Horse-5-333/twins/gerber-drill/twins-left/yg/GBR_8921560_1_snapshot.png

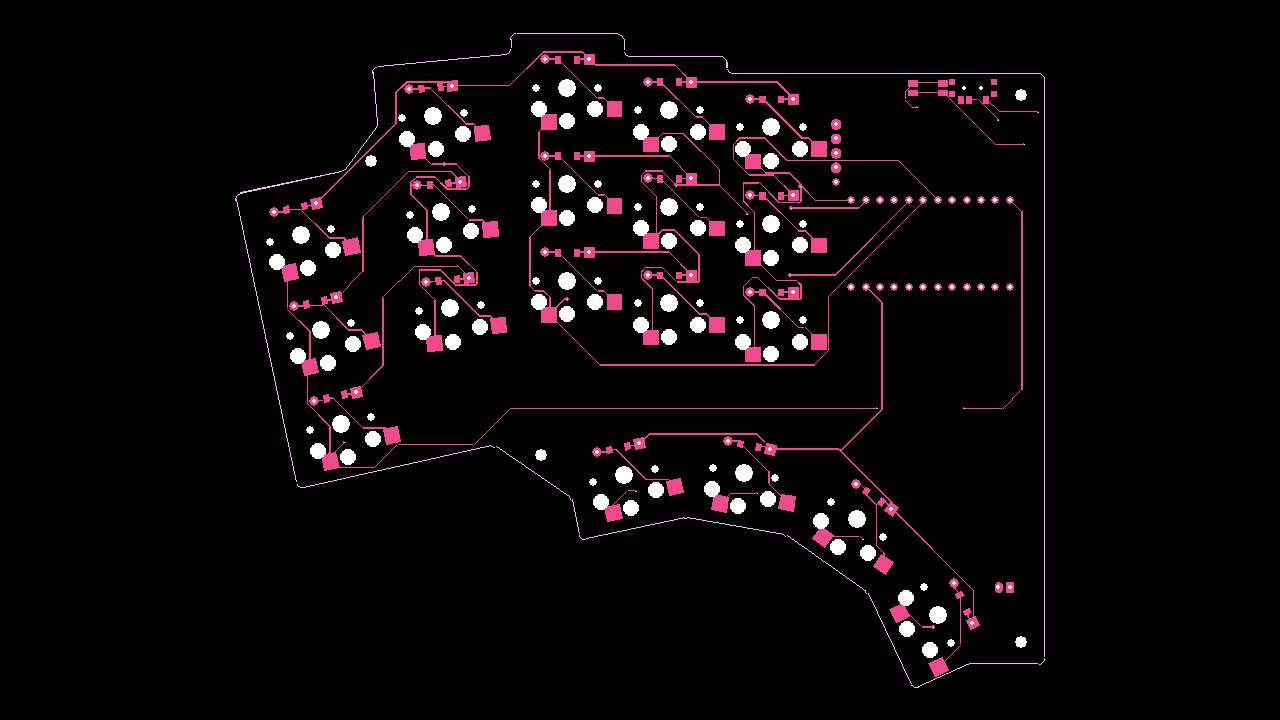
gerber-drill/twins-left/yg/GBR_8921560_1_snapshot.png
