Horse-5-333/twins/IMG_1064.jpeg

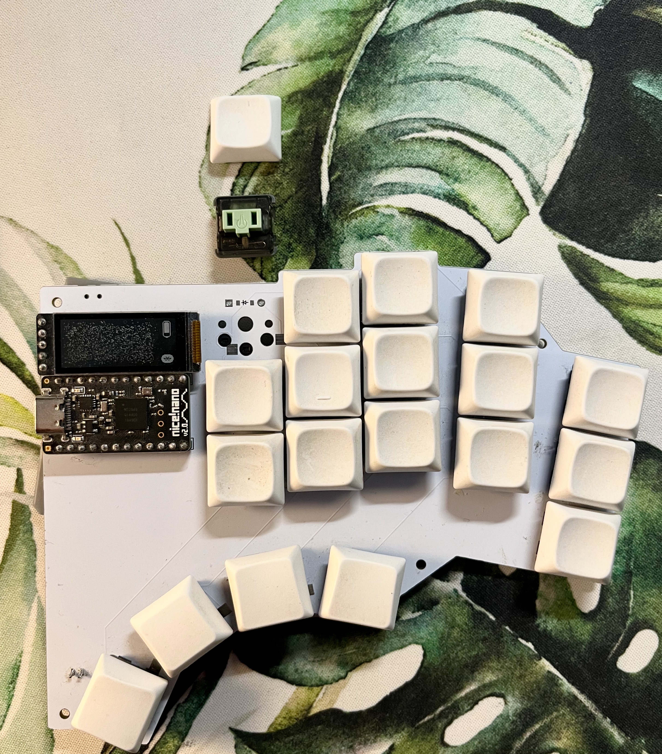
IMG_1064.jpeg
